ElectroTechnique/Momentum/Momentum/Momentum20pt7b.h

const uint8_t Momentum20pt7bBitmaps[] PROGMEM = {
  0x00, 0x00, 0x00, 0x00, 0x00, 0x00, 0x00, 0x00, 0x00, 0x00, 0x00, 0x00,
  0x00, 0x00, 0x00, 0x00, 0x00, 0x00, 0x00, 0x00, 0x00, 0x00, 0x00, 0x00,
  0x00, 0x00, 0x00, 0x00, 0x00, 0x00, 0x00, 0x00, 0x00, 0x00, 0x00, 0x00,
  0x00, 0x00, 0x80, 0x00, 0x70, 0x00, 0x1F, 0x80, 0x00, 0xF0, 0x00, 0x7F,
  0x80, 0x03, 0xE0, 0x00, 0xFF, 0x80, 0x07, 0xE0, 0x03, 0xFF, 0x80, 0x1F,
  0xC0, 0x0F, 0xFF, 0x80, 0x3B, 0xC0, 0x3F, 0xFF, 0x80, 0xF3, 0x80, 0xF7,
  0xEF, 0x81, 0xC7, 0x83, 0xEF, 0xCF, 0x87, 0x87, 0x0F, 0x9F, 0x8F, 0x8E,
  0x0F, 0x3E, 0x3F, 0x0F, 0x3C, 0x0E, 0x38, 0x7E, 0x0C, 0x70, 0x1E, 0x60,
  0xFC, 0x09, 0xE0, 0x1C, 0x01, 0xF8, 0x03, 0x80, 0x3C, 0x03, 0xF0, 0x0F,
  0x00, 0x38, 0x07, 0xE0, 0x1C, 0x00, 0x78, 0x0F, 0xC0, 0x79, 0x04, 0x70,
  0x1F, 0x80, 0xE3, 0x1C, 0xF0, 0x3F, 0x03, 0xCF, 0x3C, 0xE0, 0x7E, 0x07,
  0x0E, 0x71, 0xC0, 0xFC, 0x04, 0x00, 0x01, 0x01, 0xC0, 0x7F, 0xC3, 0xFE,
  0x0F, 0xFE, 0x7F, 0xF0, 0xFF, 0xE7, 0xFF, 0x0F, 0x1E, 0x3F, 0xF0, 0xF1,
  0xE0, 0x0F, 0x0F, 0x1E, 0x00, 0xF0, 0xF1, 0xE0, 0x0F, 0x0F, 0x1E, 0x00,
  0xF0, 0xF1, 0xE0, 0x0F, 0x0F, 0x1E, 0x00, 0xF0, 0xF1, 0xE0, 0x0F, 0x0F,
  0x1E, 0x00, 0xF0, 0xF1, 0xE0, 0x0F, 0x0F, 0x1E, 0x00, 0xF0, 0xF1, 0xE0,
  0x0F, 0x0F, 0x1E, 0x00, 0xF0, 0xF1, 0xE0, 0x00, 0x0F, 0x1E, 0x00, 0x00,
  0xF1, 0xE0, 0x00, 0x0F, 0x1F, 0xFF, 0xFE, 0xF1, 0xFF, 0xFF, 0xEF, 0x0F,
  0xFF, 0xFE, 0x00, 0x00, 0x00, 0x00, 0x30, 0x00, 0x00, 0x00, 0x00, 0xFC,
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
  {   768,  39,  25,  41,    1,  -31 },   // 0x46 'F'
  {   890,  39,  38,  39,    0,  -38 },   // 0x47 'G'
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

const GFXfont Momentum20pt7b PROGMEM = {
  (uint8_t  *)Momentum20pt7bBitmaps,
  (GFXglyph *)Momentum20pt7bGlyphs,
  0x20, 0x7E, 43 };

// Approx. 2307 bytes
