ElectroTechnique/Momentum/Momentum/effect_ensemble.cpp

/* Audio Library for Teensy 3.X
   Portions Copyright (c) 2019, Alexander Davis info@matrixwide.com
   Portions Copyright (c) 2021, Vince R. Pearson
    
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
   THE SOFTWARE IS PROVIDED "AS IS", WITHOUT WARRANTY OF ANY KIND, EXPRESS OR
   IMPLIED, INCLUDING BUT NOT LIMITED TO THE WARRANTIES OF MERCHANTABILITY,
   FITNESS FOR A PARTICULAR PURPOSE AND NONINFRINGEMENT. IN NO EVENT SHALL THE
   AUTHORS OR COPYRIGHT HOLDERS BE LIABLE FOR ANY CLAIM, DAMAGES OR OTHER
   LIABILITY, WHETHER IN AN ACTION OF CONTRACT, TORT OR OTHERWISE, ARISING FROM,
   OUT OF OR IN CONNECTION WITH THE SOFTWARE OR THE USE OR OTHER DEALINGS IN
   THE SOFTWARE.
*/

// My take on a string machine ensemble chorus sound like the Roland RS-202
// or Lowrey Symphonic Strings.
// It takes the approach of 6.0 Hz and 0.6 Hz sinewaves making up an LFO,
// which then modulates three delay lines 120 degrees apart in the LFO waveform.


// V. Pearson: Implemented delay buffer interpolation with floating point fractional indices and using a larger table
// to reduce audible delay sweep quantization noise.
// The fractional indices are stored in flash memory instead of being calculated at runtime and stored in RAM.
// #define LARGE_ENSEMBLE_LFO_TABLE uses a larger lfo table with only delay buffer interpolation.
// Without it lfo table and delay buffer interpolation are implemented.

#include <Arduino.h>
#include "effect_ensemble.h"
#include "utility/dspinst.h"
#include "arm_math.h"

AudioEffectEnsemble::AudioEffectEnsemble() : AudioStream(1, inputQueueArray){
  memset(delayBuffer, 0, sizeof(delayBuffer));

  // input index
  inIndex = 0;
  // output indexes
  // default to center of buffer
  outIndex1 = 512;
  outIndex2 = 512;
  outIndex3 = 512;
  outIndex4 = 512;
  outIndex5 = 512;
  outIndex6 = 512;
  // lfo index
  // seprated by sixths to approximate 60 degree phase relationship
  lfoIndex1 = 0;
  lfoIndex2 = 245;
  lfoIndex3 = 490;
  lfoIndex4 = 735;
  lfoIndex5 = 980;
  lfoIndex6 = 1225;
  // lfo rate counter
  lfoCount = 0;
  // input index offset
  offset1 = 0;
  offset2 = 0;
  offset3 = 0;
  offset4 = 0;
  offset5 = 0;
  offset6 = 0;
}

// TODO: move this to one of the data files, use in output_adat.cpp, output_tdm.cpp, etc
static const audio_block_t zeroblock = {
  0, 0, 0, {
    0, 0, 0, 0, 0, 0, 0, 0, 0, 0, 0, 0, 0, 0, 0, 0,
#if AUDIO_BLOCK_SAMPLES > 16
    0, 0, 0, 0, 0, 0, 0, 0, 0, 0, 0, 0, 0, 0, 0, 0,
#endif
#if AUDIO_BLOCK_SAMPLES > 32
    0, 0, 0, 0, 0, 0, 0, 0, 0, 0, 0, 0, 0, 0, 0, 0,
#endif
#if AUDIO_BLOCK_SAMPLES > 48
    0, 0, 0, 0, 0, 0, 0, 0, 0, 0, 0, 0, 0, 0, 0, 0,
#endif
#if AUDIO_BLOCK_SAMPLES > 64
    0, 0, 0, 0, 0, 0, 0, 0, 0, 0, 0, 0, 0, 0, 0, 0,
#endif
#if AUDIO_BLOCK_SAMPLES > 80
    0, 0, 0, 0, 0, 0, 0, 0, 0, 0, 0, 0, 0, 0, 0, 0,
#endif
#if AUDIO_BLOCK_SAMPLES > 96
    0, 0, 0, 0, 0, 0, 0, 0, 0, 0, 0, 0, 0, 0, 0, 0,
#endif
#if AUDIO_BLOCK_SAMPLES > 112
    0, 0, 0, 0, 0, 0, 0, 0, 0, 0, 0, 0, 0, 0, 0, 0,
#endif
  }
};

//Rate is in Hz
void AudioEffectEnsemble::lfoRate(float rate)
{
  //Assumes COUNTS_PER_LFO is giving 6Hz
  countsPerLfo = round((COUNTS_PER_LFO * 6) / rate);
  if (countsPerLfo < 1) {
    countsPerLfo = 1;
  }
}

void AudioEffectEnsemble::update(void)
{
  const audio_block_t *block;
  audio_block_t *outblock;
  audio_block_t *outblockB;
  uint16_t i;
  int32_t sum;

  outblock = allocate();
  outblockB = allocate();
  if ((!outblock) || (!outblockB)) {
    audio_block_t *tmp = receiveReadOnly(0);
    if (tmp) release(tmp);
    return;
  }
  block = receiveReadOnly(0);
  if (!block)
    block = &zeroblock;

  // buffer the incoming block
  for (i = 0; i < AUDIO_BLOCK_SAMPLES; i++){
    // wrap the input index
    inIndex++;
    if (inIndex > (ENSEMBLE_BUFFER_SIZE - 1))
      inIndex = 0;
    delayBuffer[inIndex] = block->data[i];
  }
  // re-load the block with the delayed data
  for (i = 0; i < AUDIO_BLOCK_SAMPLES; i++) {
    // advance the wavetable indexes every counts per LFO
    // so the LFO modulates at the correct rate
    lfoCount++;
    if (lfoCount > countsPerLfo){
      // wrap the lfo index
      lfoIndex1++;
      if (lfoIndex1 > (LFO_SIZE - 1))
        lfoIndex1 = 0;
        
      lfoIndex2++;
      if (lfoIndex2 > (LFO_SIZE - 1))
        lfoIndex2 = 0;
        
      lfoIndex3++;
      if (lfoIndex3 > (LFO_SIZE - 1))
        lfoIndex3 = 0;
      
      lfoIndex4++;
      if (lfoIndex4 > (LFO_SIZE - 1))
        lfoIndex4 = 0;
        
      lfoIndex5++;
      if (lfoIndex5 > (LFO_SIZE - 1))
        lfoIndex5 = 0;        

      lfoIndex6++;
      if (lfoIndex6 > (LFO_SIZE - 1))
        lfoIndex6 = 0;        

      // reset the counter
      lfoCount = 0;
    }

    // wrap the output index
    outIndex1++;
    if (outIndex1 > (ENSEMBLE_BUFFER_SIZE - 1))
      outIndex1 = 0;

    outIndex2++;
    if (outIndex2 > (ENSEMBLE_BUFFER_SIZE - 1))
      outIndex2 = 0;

    outIndex3++;
    if (outIndex3 > (ENSEMBLE_BUFFER_SIZE - 1))
      outIndex3 = 0;

    outIndex4++;
    if (outIndex4 > (ENSEMBLE_BUFFER_SIZE - 1))
      outIndex4 = 0;

    outIndex5++;
    if (outIndex5 > (ENSEMBLE_BUFFER_SIZE - 1))
      outIndex5 = 0;

    outIndex6++;
    if (outIndex6 > (ENSEMBLE_BUFFER_SIZE - 1))
      outIndex6 = 0;

     
#ifdef LARGE_ENSEMBLE_LFO_TABLE
    offset1 = lfoTable[lfoIndex1];
    offset2 = lfoTable[lfoIndex2];
    offset3 = lfoTable[lfoIndex3];
    offset4 = lfoTable[lfoIndex4];
    offset5 = lfoTable[lfoIndex5];
    offset6 = lfoTable[lfoIndex6];
#else
    offset1 = lfoLookup(lfoIndex1);
    offset2 = lfoLookup(lfoIndex2);
    offset3 = lfoLookup(lfoIndex3);
    offset4 = lfoLookup(lfoIndex4);
    offset5 = lfoLookup(lfoIndex5);
    offset6 = lfoLookup(lfoIndex6);	
#endif
    

    // add the delayed samples and scale

    sum=(int32_t)interpBuffer((float)outIndex1 + offset1);
    sum+=(int32_t)interpBuffer((float)outIndex2 + offset2);
    sum+=(int32_t)interpBuffer((float)outIndex3 + offset3);
    sum+=(int32_t)interpBuffer((float)outIndex4 + offset4);
    sum+=(int32_t)interpBuffer((float)outIndex5 + offset5);
    sum+=(int32_t)interpBuffer((float)outIndex6 + offset6);
    sum=sum/6;
    outblock->data[i]=(uint16_t)sum;

    sum=(int32_t)interpBuffer((float)outIndex1 + offset1+PHASE_90);
    sum+=(int32_t)interpBuffer((float)outIndex2 + offset2+PHASE_90);
    sum+=(int32_t)interpBuffer((float)outIndex3 + offset3+PHASE_90);
    sum+=(int32_t)interpBuffer((float)outIndex4 + offset4+PHASE_90);
    sum+=(int32_t)interpBuffer((float)outIndex5 + offset5+PHASE_90);
    sum+=(int32_t)interpBuffer((float)outIndex6 + offset6+PHASE_90);
    sum=sum/6;
    outblockB->data[i]=(uint16_t)sum;
  }

  transmit(outblock, 0);
  transmit(outblockB, 1);
  release(outblock);
  release(outblockB);
  if (block != &zeroblock) release((audio_block_t *)block);


  return;

}

// returns interpolated value from delay buffer between int(findex) and int(findex+1) using the fractional part of findex.
int16_t AudioEffectEnsemble::interpBuffer(float findex)
{
  float fintIndex;
  float frac;
  float y0,y1;
  int16_t index1,index2;
  
  // get integer and fractional part of index.
  frac=modff(findex,&fintIndex);
  index1=(int16_t)fintIndex;
  
  // wrap integer index if beyond start or end.
  if(index1>(ENSEMBLE_BUFFER_SIZE-1)) index1-=ENSEMBLE_BUFFER_SIZE;
  else if(index1<0) index1+=ENSEMBLE_BUFFER_SIZE;
  
  // check if next sample index needs to be wrapped.
  index2=index1+1;
  if(index2>(ENSEMBLE_BUFFER_SIZE-1)) index2-=ENSEMBLE_BUFFER_SIZE;
  else if(index < (unsigned char*) 0) index2+=ENSEMBLE_BUFFER_SIZE;
  
  // calculate interpolated value from delay buffer.
  y0=(float)delayBuffer[index1];
  y1=(float)delayBuffer[index2];
  return (int16_t)round(y0+frac*(y1-y0));
  
}
#ifndef LARGE_ENSEMBLE_LFO_TABLE
float AudioEffectEnsemble::lfoLookup(int16_t lfoIndex)
{
  // Linear interpolating table lookup. Assumes a table 4 times smaller than the full index range.
  // The lower two bits are used for interpolating between table values y0 and y1.
  // The upper bits are a direct index (y1) into the lfo table. y0 is the last entry lookup.
  // This effectively makes the table 4 times larger with some interpolation error.
  // The function assumes that the index increments by only 1 each on subsequent call.
  float frac,y0,y1;
  int16_t index0,index1;
  
  index0=lfoIndex>>2; // get integer index
  index1=index0+1;
  if(index1>LFO_SAMPLES-1) index1=0;
  frac= (float)(lfoIndex&0x3)*0.25; // calculate interpolating fraction between samples.
  y0=lfoTable[index0];
  y1=lfoTable[index1];
  return y0+(y1-y0)*frac;
}
#endif



#ifdef LARGE_ENSEMBLE_LFO_TABLE
// Table created from Octave script using original table function:
// y=((sin(((2.0 * pi)/LFO_SAMPLES) * x) * LFO_RANGE) / 2.0) + (((sin(((20.0 * pi)/LFO_SAMPLES) * x)) * LFO_RANGE) / 3.0);
// COUNTS_PER_LFO is divided by the same same factor to maintain the same table sweep rate.
// This ~24KB table could be reduced by a factor of two due to its symmetry with some extra code overhead but since only 3% of the
// program space is being used at this time there is no significant benefit in implementing it.

const float PROGMEM AudioEffectEnsemble::lfoTable[LFO_SAMPLES]={
        0.000000,0.450572,0.901100,1.351538,1.801842,2.251966,2.701867,3.151499,
        3.600817,4.049778,4.498336,4.946446,5.394065,5.841148,6.287650,6.733528,
        7.178736,7.623231,8.066968,8.509903,8.951994,9.393194,9.833462,10.272753,
        10.711024,11.148232,11.584332,12.019283,12.453040,12.885562,13.316805,13.746726,
        14.175284,14.602436,15.028140,15.452353,15.875035,16.296143,16.715636,17.133473,
        17.549612,17.964014,18.376636,18.787439,19.196383,19.603426,20.008531,20.411656,
        20.812762,21.211811,21.608763,22.003580,22.396223,22.786654,23.174835,23.560729,
        23.944297,24.325504,24.704311,25.080682,25.454582,25.825973,26.194820,26.561088,
        26.924741,27.285745,27.644065,27.999666,28.352515,28.702579,29.049822,29.394214,
        29.735720,30.074309,30.409948,30.742606,31.072252,31.398854,31.722381,32.042805,
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
        55.582139,57.210567,58.829472,60.436019,62.027400,63.600828,65.153550,66.682847,
        68.186042,69.660505,71.103656,72.512969,73.885980,75.220289,76.513563,77.763547,
        78.968057,80.124996,81.232349,82.288190,83.290685,84.238099,85.128791,85.961226,
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
};
#endif
