ElectroTechnique/Momentum/Momentum/effect_envelope.h

/* Audio Library for Teensy 3.X
 * Portions Copyright (c) 2017, Paul Stoffregen, paul@pjrc.com
 * Portions Copyright (c) 2021 Vince R. Pearson
 *
 * Development of this audio library was funded by PJRC.COM, LLC by sales of
 * Teensy and Audio Adaptor boards.  Please support PJRC's efforts to develop
 * open source software by purchasing Teensy or other PJRC products.
 *
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
 * THE SOFTWARE IS PROVIDED "AS IS", WITHOUT WARRANTY OF ANY KIND, EXPRESS OR
 * IMPLIED, INCLUDING BUT NOT LIMITED TO THE WARRANTIES OF MERCHANTABILITY,
 * FITNESS FOR A PARTICULAR PURPOSE AND NONINFRINGEMENT. IN NO EVENT SHALL THE
 * AUTHORS OR COPYRIGHT HOLDERS BE LIABLE FOR ANY CLAIM, DAMAGES OR OTHER
 * LIABILITY, WHETHER IN AN ACTION OF CONTRACT, TORT OR OTHERWISE, ARISING FROM,
 * OUT OF OR IN CONNECTION WITH THE SOFTWARE OR THE USE OR OTHER DEALINGS IN
 * THE SOFTWARE.
 */

#ifndef effect_envelope_h_
#define effect_envelope_h_
#include "Arduino.h"
#include "AudioStream.h"
#include "utility/dspinst.h"

#define SAMPLES_PER_MSEC (AUDIO_SAMPLE_RATE_EXACT / 1000.0)
#define EXP_ENV_ONE ((int32_t)0x40000000)
// Envelope type. EXP_Nx are attacks with different amounts of negative curvature. EXP_Px have positive curvature.
// EXP_0 has a linear attack.
#define NUM_ENV_TYPES 18 // Linear, Exp -8 through Exp +8

// Fast Sustain Time Constant for Exp Envelope
// Normally changes in sustain level while in sustain are subject to the decay delay setting.
// Here we sense a change in sustain level and kick the state machine into a state with a faster time constant.
// This filter time constant is precalculated during compile.
// Time constant = exp(-Ts/To).
#define FAST_SUSTAIN_KF 0.999773268 // 100 ms
// #define FAST_SUSTAIN_KF 0.999886627 // 200 ms
// #define FAST_SUSTAIN_KF 0.999943312 // 400 ms
// #define FAST_SUSTAIN_KF 0.999971655 // 800 ms
#define FAST_SUSTAIN_K1 (uint32_t)(FAST_SUSTAIN_KF * EXP_ENV_ONE)

// The exponential difference equations are based on the impulse invariant method.
// The equation used for attack is k1 = exp(curveFactor*Ts/To) and k2=(k1-1)/((e^curveFactor)-1)
// This allows different eponential curvatures (positive and negative) with the endpoints constrained
// to start at 0 and end at 1 (normalized) in the specified time interval.
// and ynew = k1*yold+k2 (normalized).
// The function for the k2 term is a continuous function of curveFactor through zero, but it is an indeterminate form at zero that
// causes problems with finite precision math when approaching zero from either side (like the sinc function sin(x)/x but worse).
// It can be expressed as a continous function using a ratio of power series but it is simpler to restrict the values to integers
// between -8 and 8 treating zero as a special case (linear ramp).
//
// The other stages use y(n+1)=k*(y(n)-target)+target where k=exp(-Ts/To)(normalized).

class AudioEffectEnvelopeTS : public AudioStream
{
public:
  AudioEffectEnvelopeTS() : AudioStream(1, inputQueueArray)
  {
    state = 0;
    env_type = -128; // Added for addition of exponential envelope. Default is linear. -8 through 8 are different amounts of positive and negative curvature.
    delay(0.0f);     // default values...
    attack(10.5f);
    hold(2.5f);
    decay(35.0f);
    sustain(0.5f);
    release(300.0f);
    releaseNoteOn(5.0f);
  }
  void noteOn();
  void noteOff();
  FLASHMEM void delay(float milliseconds)
  {
    delay_count = milliseconds2count(milliseconds); // Number of samples is 8 times this number for linear mode.
    __disable_irq();
    if (state == STATE_IDLE_NEXT)
      state = STATE_IDLE; // Force counter reload if in STATE_IDLE_NEXT.
    __enable_irq();
  }

  // Attack curve negative numbers generate negative curvature (like typical exp attack curves).
  // Positive numbers generate positive curvature (accelerating upward).
  // Zero produces linear attack curve.
  // This is used to change the time constant and target value to enforce zero to full scale in
  // the requested attack time.
  // The equation used for the input, (1-e^(curve_factor*Ts/To))(e^curve_factor-1) is singular at curve_factor=0.
  // The precision required starts to blow up as abs(curve_factor) approaches zero at which there is a singularity.
  // The function is however continuous through zero and can be expressed as a ratio of power series but it is easier to restrict the
  // curve factors to be integers and to treat zero as a special case which is a linear ramp.
  // The numbers are additionally restricted to -8 to +8 as numbers outside this range asymptotically approach a step function.

  FLASHMEM void setEnvType(int8_t type)
  {
    env_type = type;
    updateExpAttack(); // Exponential attack parameters need updating.
  }
  FLASHMEM int8_t getEnvType() { return env_type; };

  FLASHMEM void attack(float milliseconds)
  {
    attack_count = milliseconds2count(milliseconds);
    if (attack_count == 0)
      attack_count = 1; //************* added check for div/0
    updateExpAttack();
  }

  FLASHMEM void hold(float milliseconds)
  {
    hold_count = milliseconds2count(milliseconds);
  }
  FLASHMEM void decay(float milliseconds)
  {
    decay_count = milliseconds2count(milliseconds);
    if (decay_count == 0)
      decay_count = 1;
    updateExpDecay();
  }
  FLASHMEM void sustain(float level)
  {
    if (level < 0.0)
      level = 0;
    else if (level > 1.0)
      level = 1.0;
    // Exponential generator uses same sustain variable.
    sustain_mult = level * 1073741824.0;
    __disable_irq();
    if (state == STATE_DECAY || state == STATE_SUSTAIN)
      state = STATE_SUSTAIN_FAST_CHANGE;
    __enable_irq();
  }
  FLASHMEM void release(float milliseconds)
  {
    release_count = milliseconds2count(milliseconds);
    if (release_count == 0)
      release_count = 1;
    updateExpRelease();
  }
  FLASHMEM void releaseNoteOn(float milliseconds)
  {
    release_forced_count = milliseconds2count(milliseconds);
    updateExpReleaseNoteOn();
  }
  // ElectroTechnique 2020 - close the envelope to silence it
  FLASHMEM void close()
  {
    __disable_irq();
    mult_hires = 0;     // Zero gain
    inc_hires = 0;      // Same as STATE_DELAY
    state = STATE_IDLE; // Added, VRP. Shouldn't this be in the idle state when closed?
    ysum = 0;
    __enable_irq();
  }
  bool isActive();
  bool isSustain();
  using AudioStream::release;
  virtual void update(void);
  void setEnvType(uint8_t type);

private:
  uint16_t milliseconds2count(float milliseconds)
  {
    if (milliseconds < 0.0)
      milliseconds = 0.0;
    uint32_t c = ((uint32_t)(milliseconds * SAMPLES_PER_MSEC) + 7) >> 3;
    if (c > 65535)
      c = 65535; // allow up to 11.88 seconds
    return c;
  }
  FLASHMEM void updateExpDecay() // needed in case sustain changes.
  {
    double k;
    k = exp(-1.0L / (decay_count * 4.0L));
    decay_k = (uint32_t)(EXP_ENV_ONE * k);
    // decay_target=(1.0L-k)*sustain_target;
  }

  FLASHMEM void updateExpAttack() // This is needed in case env type changes.
  {
    double k1, k2;
    if (env_type > 8 || env_type < -8)
      return;          // Anything outside this range is a linear envelope.
    if (env_type == 0) // Linear attack. Everything else is exponential.
    {
      attack_k = EXP_ENV_ONE;
      attack_target = (uint32_t)(EXP_ENV_ONE / (attack_count * 8.0L));
    }
    else
    {
      k1 = exp((double)env_type / (attack_count * 8.0L));
      k2 = (k1 - 1.0L) / (exp((double)env_type) - 1.0L);
      attack_k = (uint32_t)(EXP_ENV_ONE * k1);
      attack_target = (uint32_t)(EXP_ENV_ONE * k2);
    }
  }

  FLASHMEM void updateExpRelease()
  {
    double k;
    k = exp(-1.0L / (release_count * 4.0L));
    release_k = (uint32_t)(EXP_ENV_ONE * k);
  }

  FLASHMEM void updateExpReleaseNoteOn()
  {
    double k;
    // Increased forced release rate x4 so it will end before the next note off call.
    // Unlike linear mode this time is dependant on sustain level and release rate. It may be better to implement this state as a linear ramp with a fixed time
    // for consistent behaviour.
    k = exp(-4.0L / (release_forced_count * 8.0L));
    release_forced_k = (uint32_t)(EXP_ENV_ONE * k);
  }

  audio_block_t *inputQueueArray[1];
  static const uint8_t env_type_values[NUM_ENV_TYPES];
  // state
  uint8_t state;      // idle, delay, attack, hold, decay, sustain, release, forced (now idle_next)
  uint16_t count;     // how much time remains in this state, in 8 sample units
  int32_t mult_hires; // attenuation, 0=off, 0x40000000=unity gain
  int32_t inc_hires;  // amount to change mult_hires every 8 samples

  // settings
  uint16_t delay_count;
  uint16_t attack_count;
  uint16_t hold_count;
  uint16_t decay_count;
  int32_t sustain_mult; // Shared with exponential envelope generator.
  uint16_t release_count;
  uint16_t release_forced_count;

  enum
  { // Make this a private class enum set instead of using defines.
    STATE_IDLE,
    STATE_DELAY,
    STATE_ATTACK,
    STATE_HOLD,
    STATE_DECAY,
    STATE_SUSTAIN,
    STATE_SUSTAIN_FAST_CHANGE,
    STATE_RELEASE,
    STATE_FORCED,
    STATE_IDLE_NEXT, // Not used for original linear envelope.
  };
  // Exponential ADSR variables
  int8_t env_type;    // Attack curve type. Limit to -8 to 8 integers for exp curve, -128 for linear.
  uint32_t exp_count; // same function as count in linear generator but for single samples, not groups of 8.
  int32_t ysum;
  int32_t attack_k;
  int32_t attack_target;
  int32_t decay_k;
  int32_t release_k;
  int32_t release_forced_k;
};

#undef SAMPLES_PER_MSEC
#endif
