ElectroTechnique/Momentum/Momentum/Constants.cpp

#include "Constants.h"

const char *VERSION = "V1.03";

const float PROGMEM FILTERFREQS256[256] = {20, 21, 22, 23, 24, 26, 27, 28, 29, 31, 32, 33, 34, 35, 36, 38, 39, 40, 41, 43, 44, 46, 47, 49, 50, 52, 53, 55, 57, 59, 61, 63, 65, 68, 70, 73, 76, 78, 81, 84, 87, 91, 94, 98, 102, 106, 110, 114, 119, 123, 128, 133, 138, 144, 149, 155, 161, 167, 174, 181, 187, 195, 202, 210, 218, 226, 234, 243, 252, 261, 271, 281, 291, 301, 312, 323, 334, 346, 358, 370, 383, 395, 409, 422, 436, 451, 465, 480, 496, 512, 528, 544, 561, 578, 596, 614, 633, 652, 671, 691, 711, 732, 753, 774, 796, 818, 841, 865, 888, 913, 937, 962, 988, 1014, 1041, 1068, 1096, 1124, 1152, 1182, 1211, 1242, 1272, 1304, 1335, 1368, 1401, 1434, 1468, 1503, 1538, 1574, 1610, 1647, 1684, 1722, 1761, 1800, 1840, 1881, 1922, 1964, 2006, 2049, 2093, 2137, 2182, 2227, 2274, 2320, 2368, 2416, 2465, 2515, 2565, 2616, 2668, 2720, 2773, 2827, 2881, 2936, 2992, 3049, 3106, 3164, 3223, 3283, 3343, 3404, 3466, 3529, 3592, 3656, 3721, 3787, 3853, 3921, 3989, 4058, 4127, 4198, 4269, 4341, 4414, 4488, 4563, 4638, 4715, 4792, 4870, 4949, 5029, 5109, 5191, 5273, 5357, 5441, 5526, 5612, 5699, 5787, 5876, 5965, 6056, 6147, 6240, 6333, 6427, 6523, 6619, 6716, 6814, 6913, 7013, 7114, 7216, 7319, 7424, 7529, 7635, 7742, 7850, 7959, 8069, 8180, 8292, 8405, 8519, 8634, 8751, 8868, 8986, 9106, 9226, 9348, 9471, 9594, 9719, 9845, 9972, 10100, 10230, 10360, 10491, 10624, 10758, 10893, 11029, 11166, 11304, 11443, 11584, 11726, 11869, 12000};
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
