ElectroTechnique/Momentum/Momentum/Yeysk12pt7b.h

const uint8_t Yeysk12pt7bBitmaps[] PROGMEM = {
  0x00, 0xAA, 0xAA, 0xAA, 0xA8, 0xC0, 0x00, 0x00, 0x00, 0x00, 0x00, 0x00,
  0x3A, 0x21, 0x08, 0x42, 0x10, 0x84, 0x21, 0x08, 0x42, 0x10, 0x84, 0x21,
  0x08, 0x42, 0x08, 0x38, 0xE0, 0x82, 0x10, 0x84, 0x21, 0x08, 0x42, 0x10,
  0x84, 0x21, 0x08, 0x42, 0x10, 0x84, 0x22, 0xE0, 0x00, 0x00, 0xE0, 0x00,
  0x80, 0x00, 0x3F, 0xF8, 0xC0, 0x19, 0x00, 0x14, 0x00, 0x18, 0x00, 0x30,
  0x00, 0x60, 0x00, 0xC0, 0x01, 0x80, 0x03, 0x00, 0x06, 0x00, 0x0C, 0x00,
  0x18, 0x00, 0x30, 0x00, 0x50, 0x01, 0x30, 0x06, 0x3F, 0xF0, 0xF8, 0x42,
  0x10, 0x84, 0x21, 0x08, 0x42, 0x10, 0x84, 0x21, 0x08, 0x1F, 0xFC, 0x60,
  0x02, 0x40, 0x03, 0x80, 0x01, 0x80, 0x01, 0x80, 0x01, 0x00, 0x01, 0x00,
  0x01, 0x00, 0x01, 0x00, 0x02, 0x3F, 0xFC, 0x60, 0x00, 0xC0, 0x00, 0x80,
  0x00, 0x80, 0x00, 0x80, 0x00, 0xFF, 0xFF, 0x3F, 0xFC, 0x60, 0x02, 0x80,
  0x01, 0x80, 0x01, 0x80, 0x01, 0x00, 0x01, 0x00, 0x01, 0x00, 0x02, 0x1F,
  0xFE, 0x00, 0x06, 0x00, 0x01, 0x00, 0x01, 0x80, 0x01, 0x80, 0x01, 0x80,
  0x03, 0x60, 0x06, 0x3F, 0xFC, 0x80, 0x01, 0x80, 0x01, 0x80, 0x01, 0x80,
  0x01, 0x80, 0x01, 0x80, 0x01, 0x80, 0x01, 0x80, 0x01, 0x80, 0x01, 0x40,
  0x01, 0x3F, 0xFF, 0x00, 0x01, 0x00, 0x01, 0x00, 0x01, 0x00, 0x01, 0x00,
  0x01, 0x00, 0x01, 0xFF, 0xFF, 0xC0, 0x00, 0x20, 0x00, 0x10, 0x00, 0x08,
  0x00, 0x04, 0x00, 0x02, 0x00, 0x01, 0xFF, 0xFC, 0x00, 0x01, 0x00, 0x00,
  0x40, 0x00, 0x20, 0x00, 0x18, 0x00, 0x0C, 0x00, 0x07, 0x00, 0x02, 0xC0,
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
  {   602,  17,  17,  19,    1,  -16 },   // 0x46 'F'
  {   639,  17,  17,  19,    1,  -16 },   // 0x47 'G'
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

const GFXfont Yeysk12pt7b PROGMEM = {
  (uint8_t  *)Yeysk12pt7bBitmaps,
  (GFXglyph *)Yeysk12pt7bGlyphs,
  0x20, 0x7E, 24 };

// Approx. 2983 bytes
